pms67/LittleBrain-STM32F4-Sensorboard/Firmware/Core/Inc/EKF.h

#ifndef EKF_H
#define EKF_H

#include <math.h>

typedef struct {

	float phi_r;
	float theta_r;

	float P[2][2];

	float Q[2];
	float R[3];

} EKF;

void EKF_Init(EKF *ekf, float P[2], float Q[2], float R[3]);

void EKF_Predict(EKF *ekf, float p_rps, float q_rps, float r_rps, float sampleTime_s);

void EKF_Update(EKF *ekf, float ax_mps2, float ay_mps2, float az_mps2);

#endif
