pms67/LittleBrain-STM32F4-Sensorboard/Firmware/Core/Inc/RCFilter.h

#ifndef RC_FILTER_H
#define RC_FILTER_H

typedef struct {

	float coeff[2];
	float out[2];

} RCFilter;

void RCFilter_Init(RCFilter *filt, float cutoffFreqHz, float sampleTimeS);
float RCFilter_Update(RCFilter *filt, float inp);

#endif
